rosatolen/DIYkey/kicad_files/key.sch

## KiCad design kicad_files/key.sch (2017-06-29)

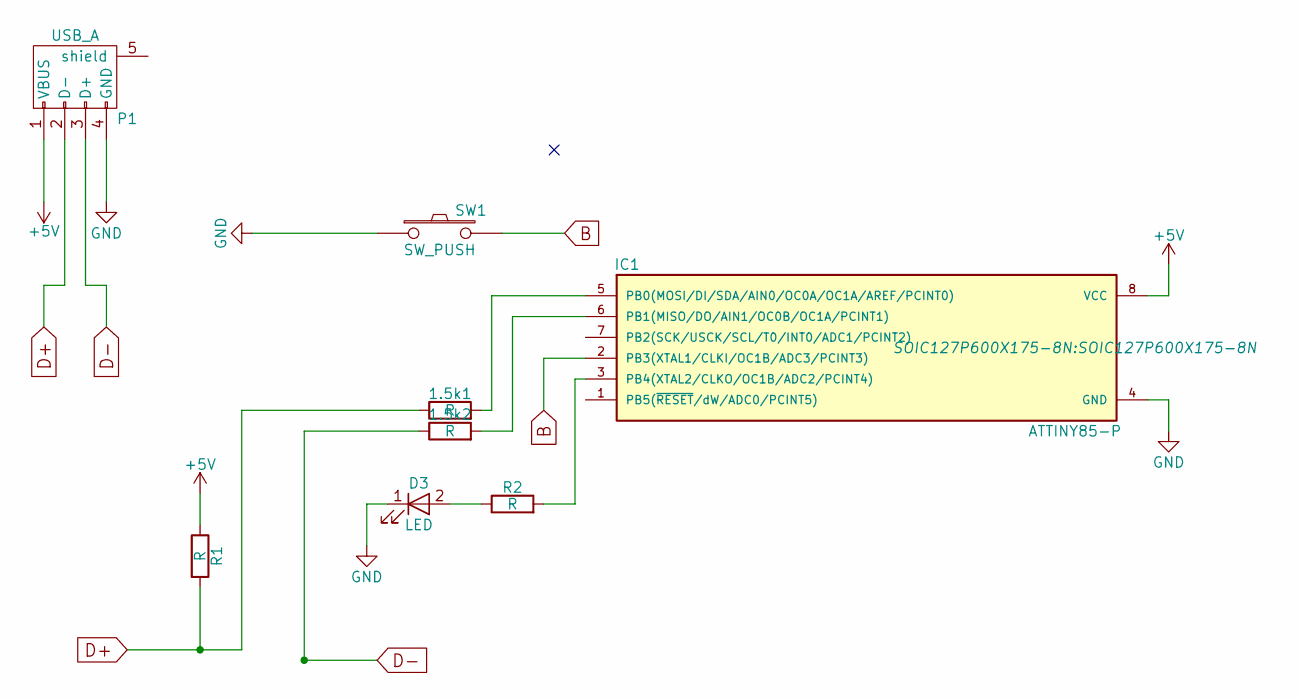
[picture p3: schematic key.sch]

Parts:
1.5k1, 1.5k2: R; R_1206
D3: LED; LED_0402
IC1: ATTINY85-P; SOIC127P600X175-8N
P1: USB_A; usb-PCB
R1, R2: R; R_1206
SW1: SW_PUSH; SW_PUSH_SMALL

Connections:
+5V: IC1.8 (VCC), P1.1 (VBUS), R1.1
B: IC1.2 (PB3(XTAL1/CLKI/OC1B/ADC3/PCINT3)), SW1.2
D+: 1.5k1.1, P1.2 (D-), R1.2
D-: 1.5k2.1, P1.3 (D+)
GND: D3.1 (K), IC1.4 (GND), P1.4 (GND), SW1.1
unnamed: 1.5k1.2, IC1.5 (PB0(MOSI/DI/SDA/AIN0/OC0A/OC1A/AREF/PCI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)
unnamed: 1.5k2.2, IC1.6 (PB1(MISO/DO/AIN1/OC0B/OC1A/PCINT1))
unnamed: D3.2 (A), R2.1
unnamed: IC1.3 (PB4(XTAL2/CLKO/OC1B/ADC2/PCINT4)), R2.2
